zuliani71/LZER0/Hardware/LCC/2021/Project.LCC/SCHEMA ELETTRICO PDF/2721022100A1.4_[No Variations]( LZER0 Core Card ).PDF

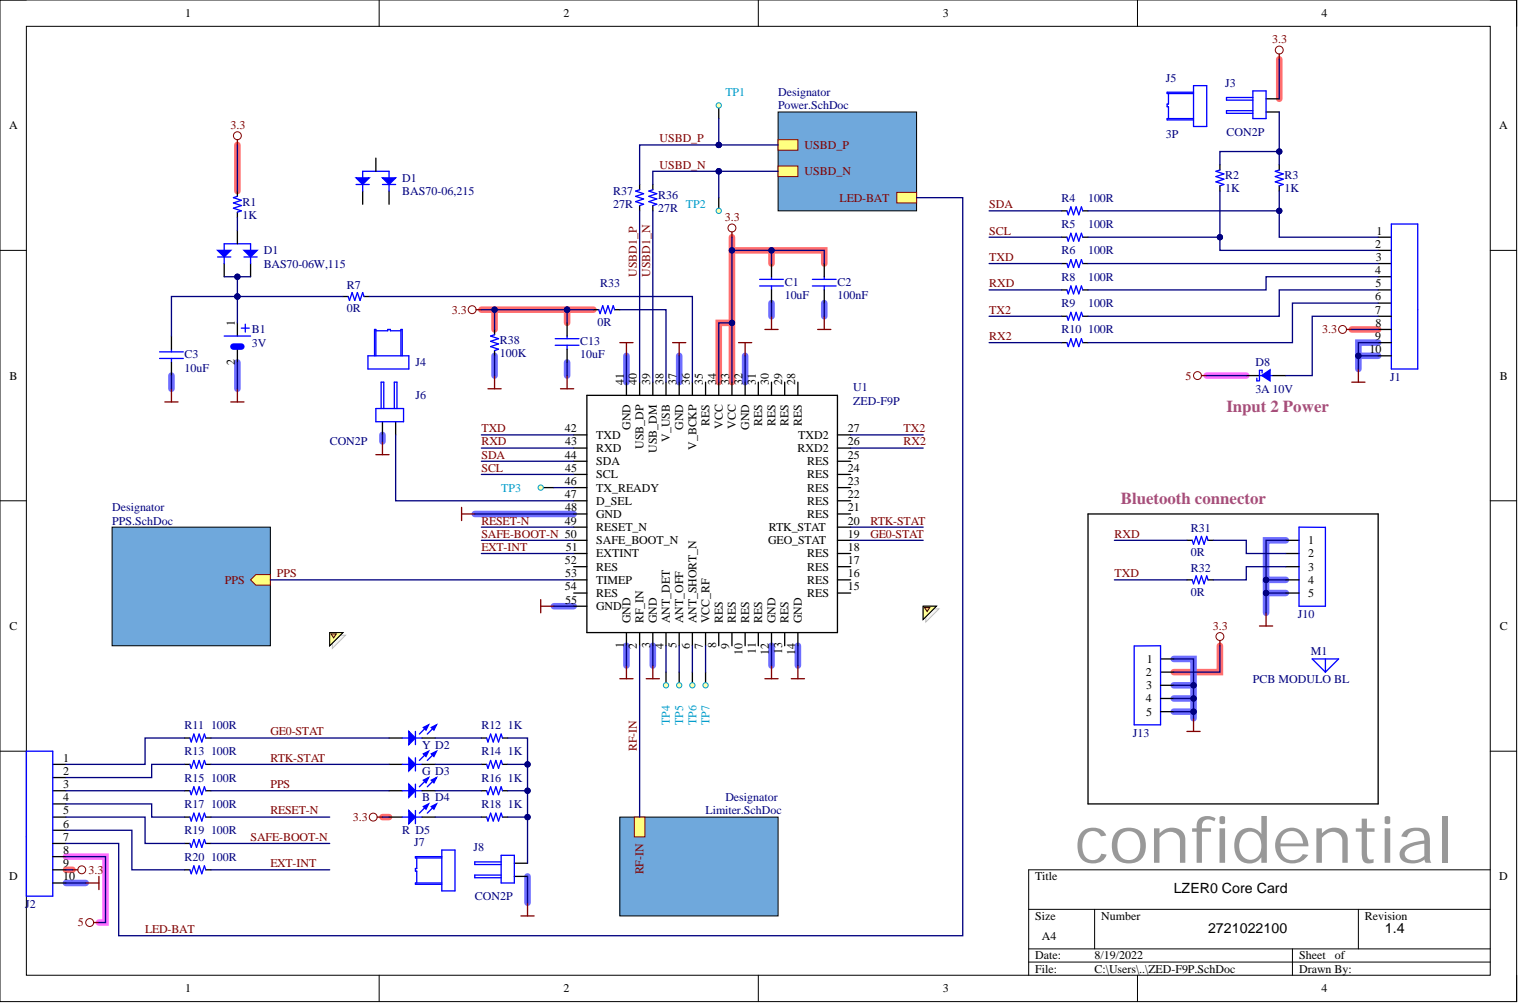
[picture p7: page 1]

GND 14 RES 15 RES 16 RES 17 RES 18

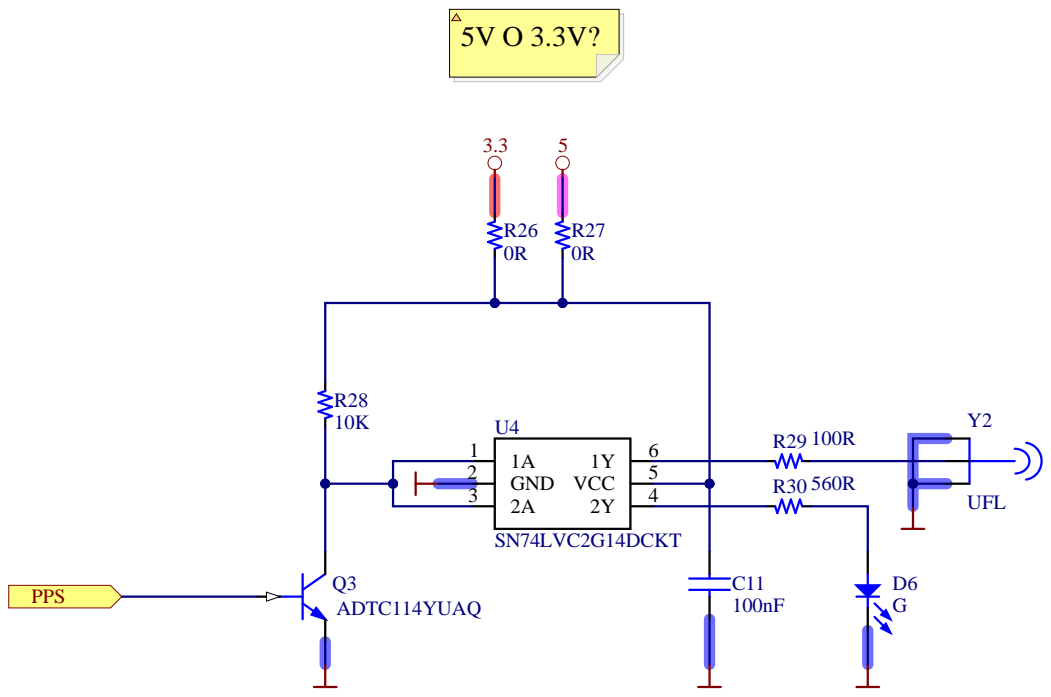
[picture p8: page 2]

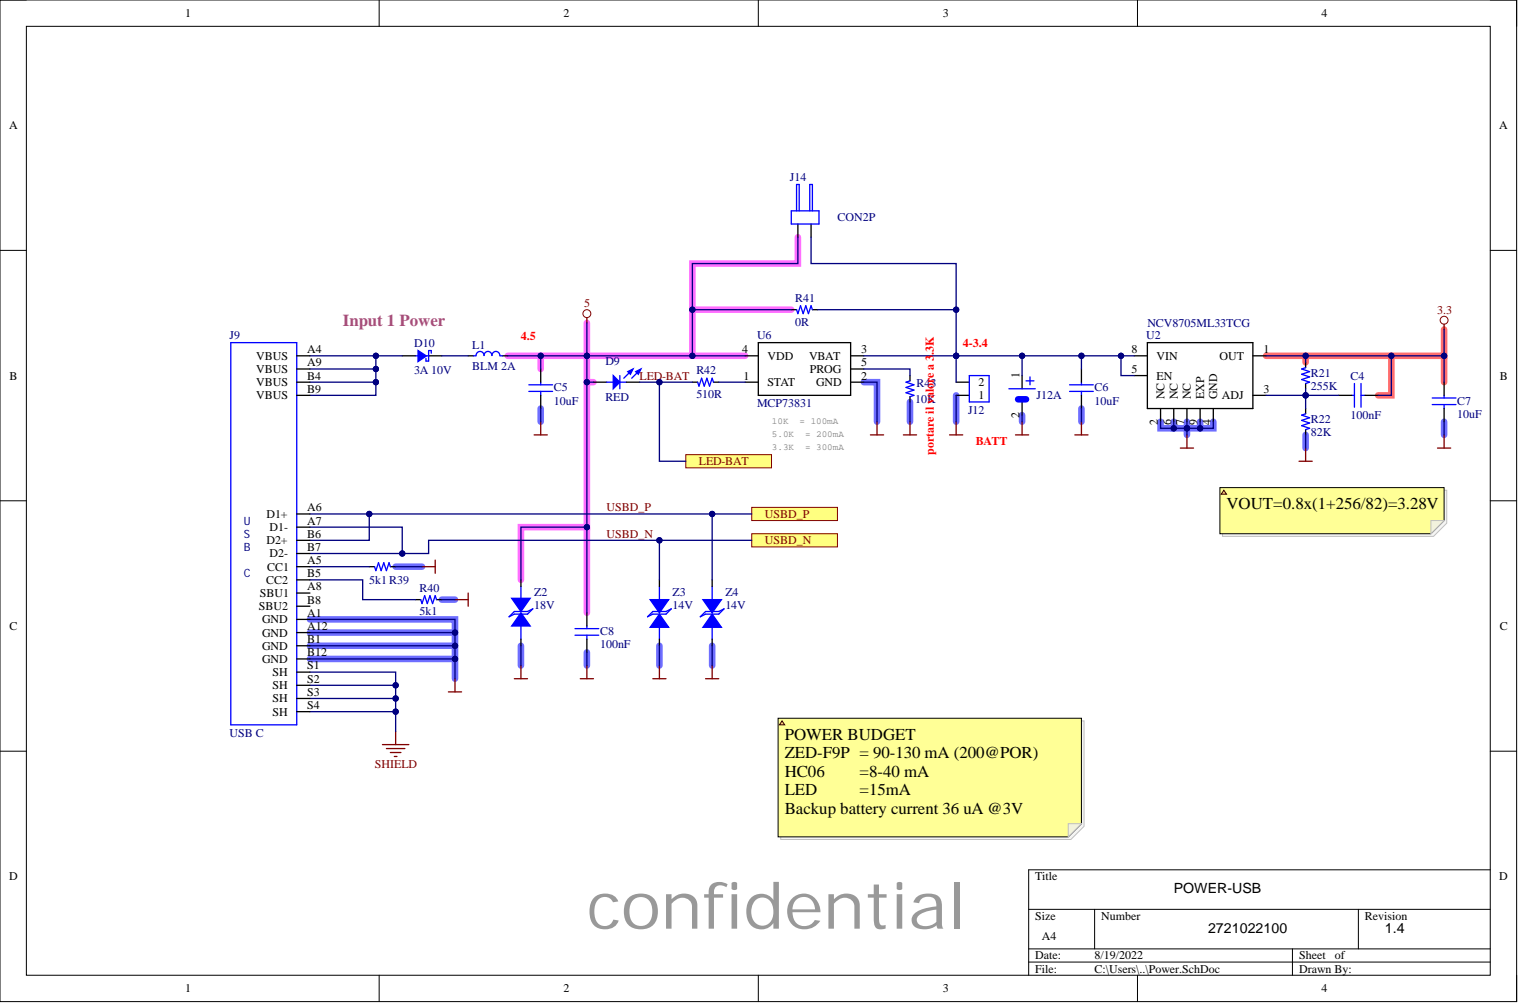
[picture p9: page 3]

POWER BUDGET
ZED-F9P = 90-130 mA (200@POR)
Backup battery current 36 uA @3V

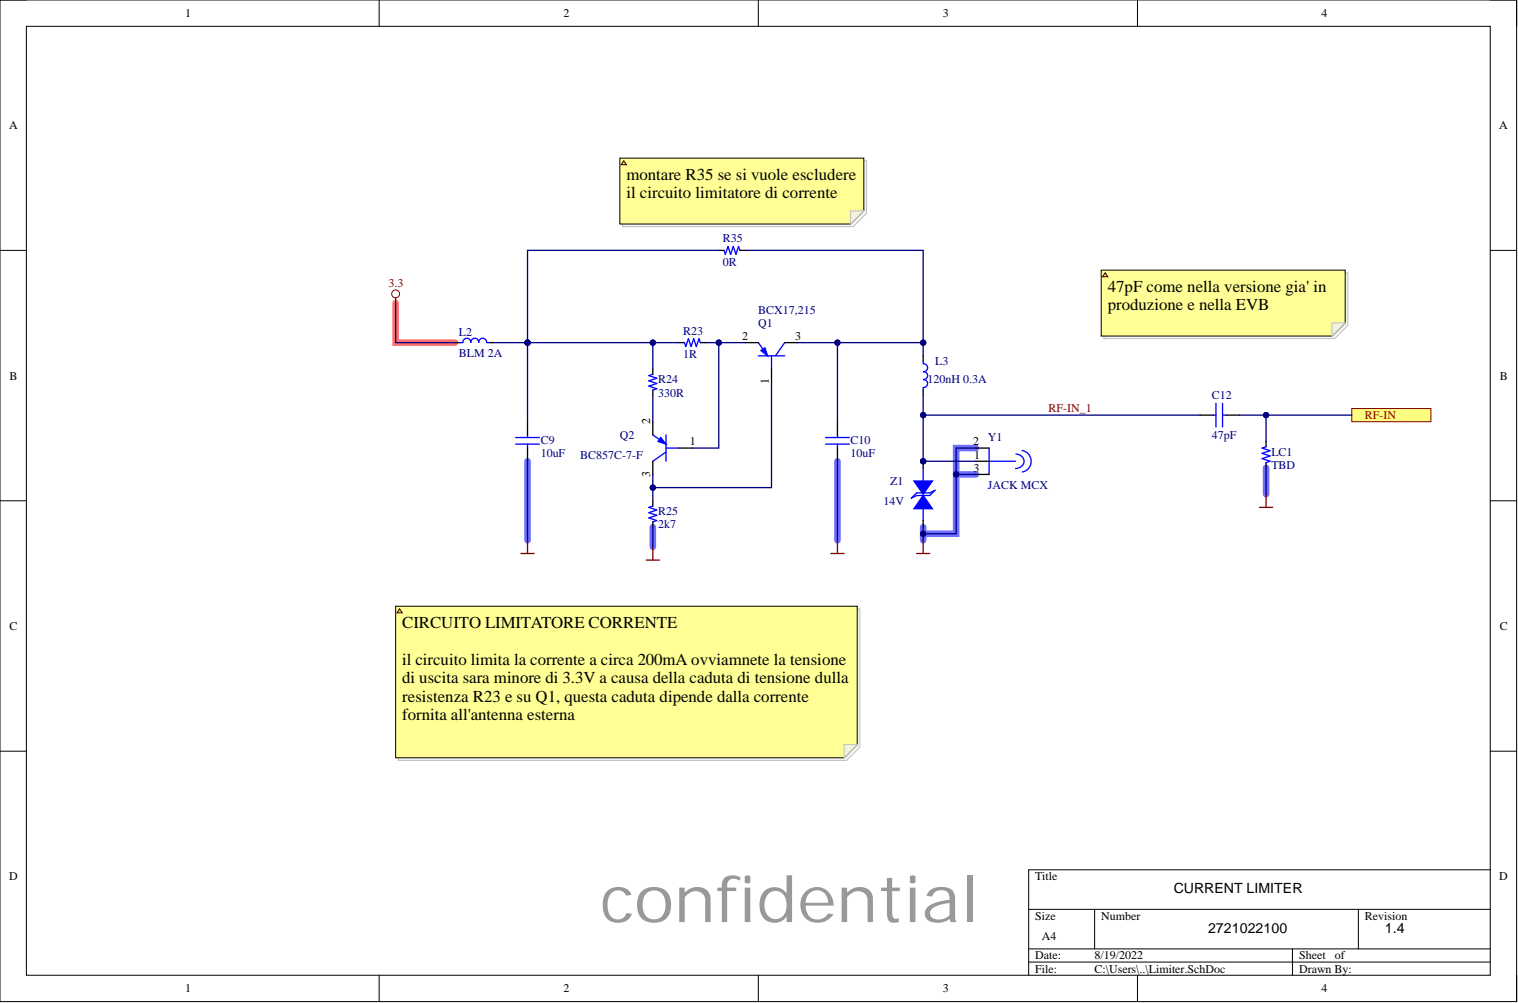
[picture p10: page 4]

montare R35 se si vuole escludere
il circuito limitatore di corrente

47pF come nella versione gia' in
produzione e nella EVB

il circuito limita la corrente a circa 200mA ovviamnete la tensione
di uscita sara minore di 3.3V a causa della caduta di tensione dulla
resistenza R23 e su Q1, questa caduta dipende dalla corrente
fornita all'antenna esterna
