zuliani71/LZER0/Hardware/LCC/2021/Project.BT.module/VARI LATI IN PDF/PCB IN PDF.PDF

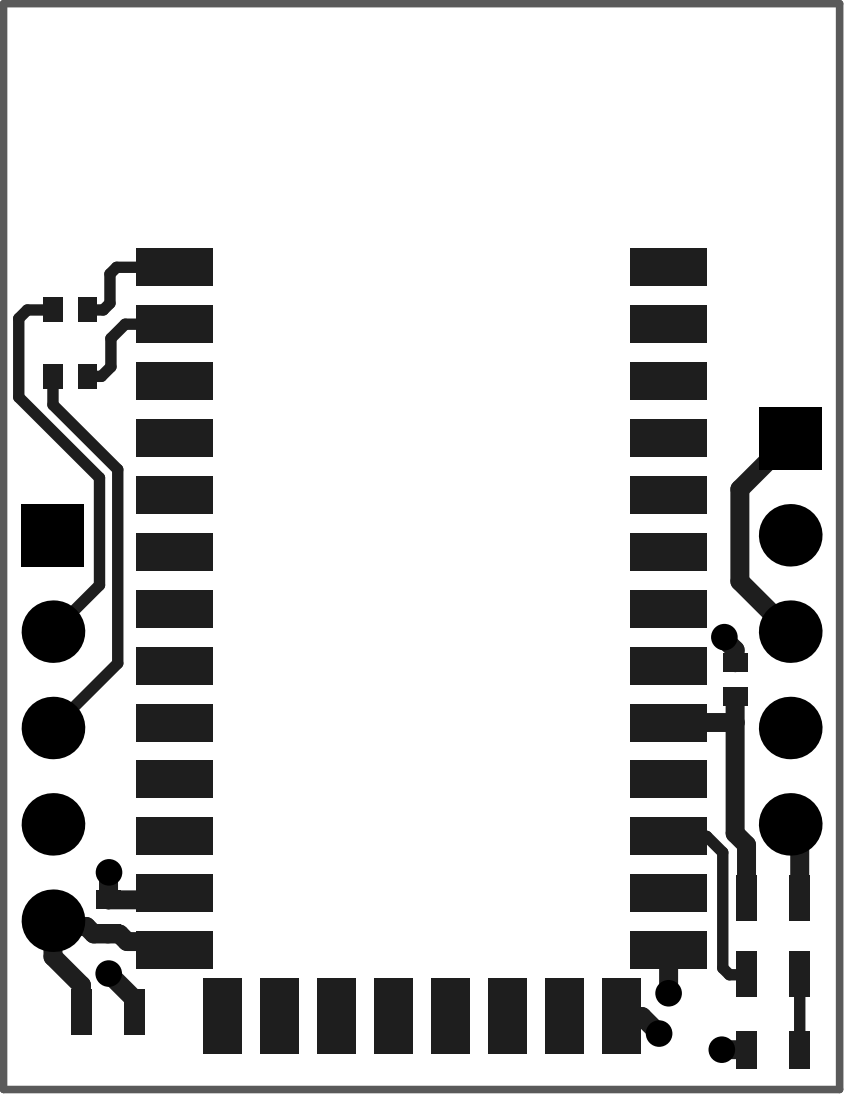
[picture p27: page 1]

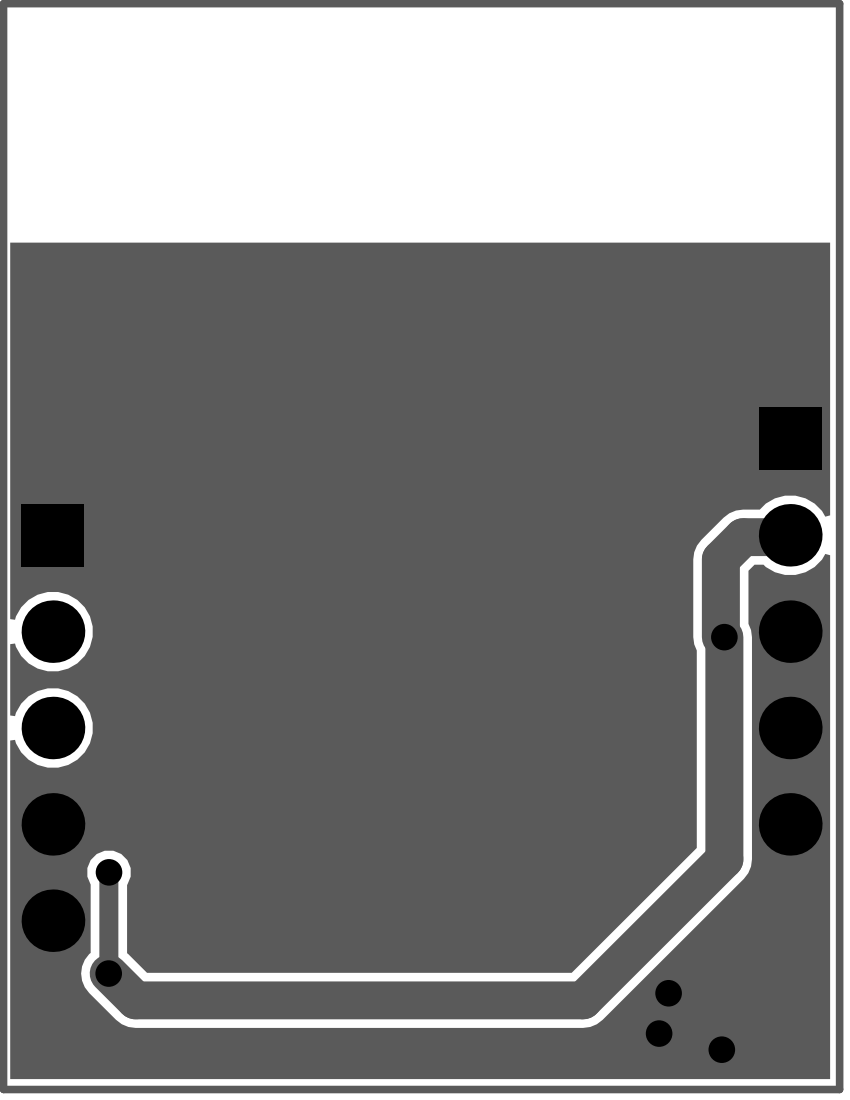
[picture p28: page 2]

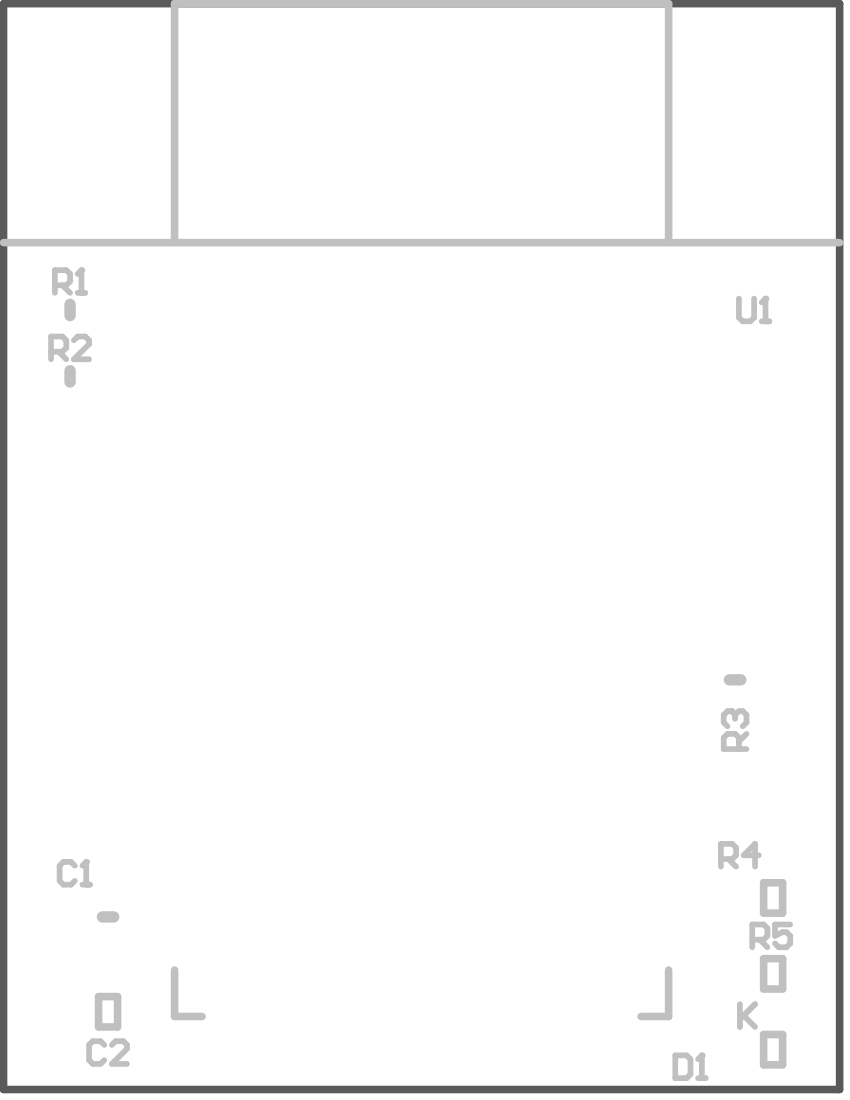
[picture p29: page 3]

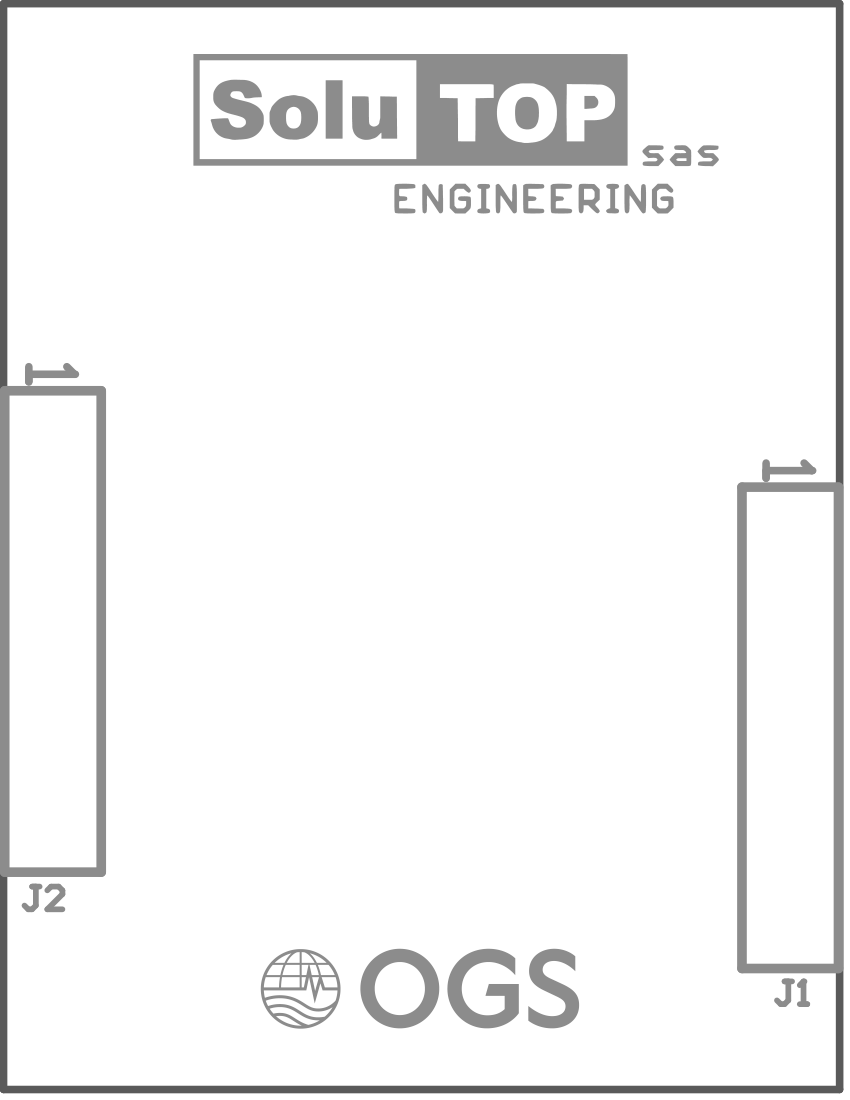
[picture p30: page 4]
