zuliani71/LZER0/Hardware/LCC/2021/Project.LCC/PIANO DI FORATURA PDF/Piano di foratura.PDF

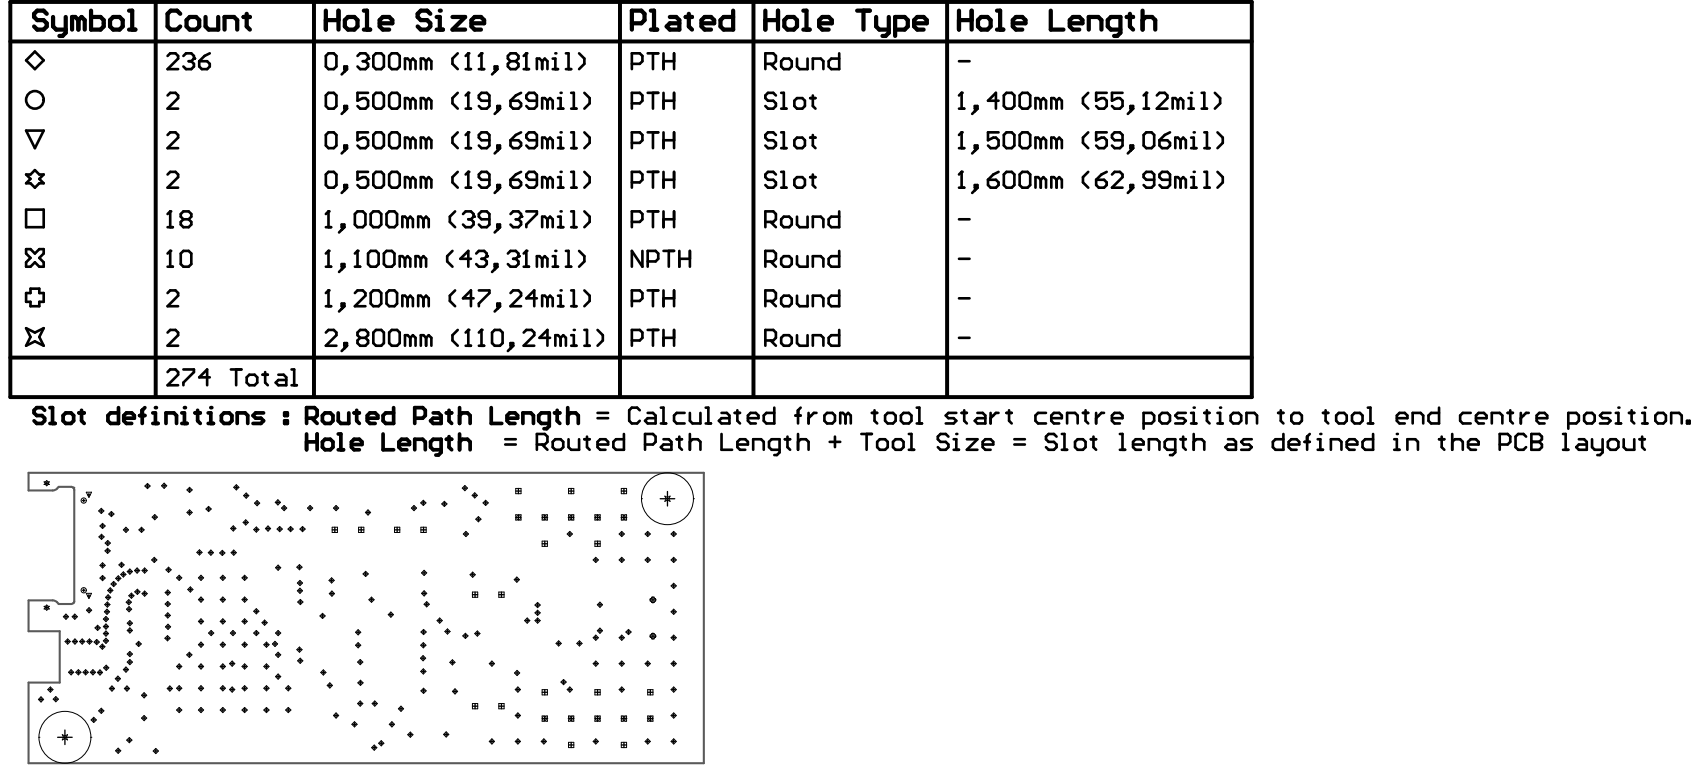
[picture p31: page 1]
