zuliani71/LZER0/Hardware/LCC/2021/Project.LCC/VARI LATI IN PDF/PCB IN PDF.PDF

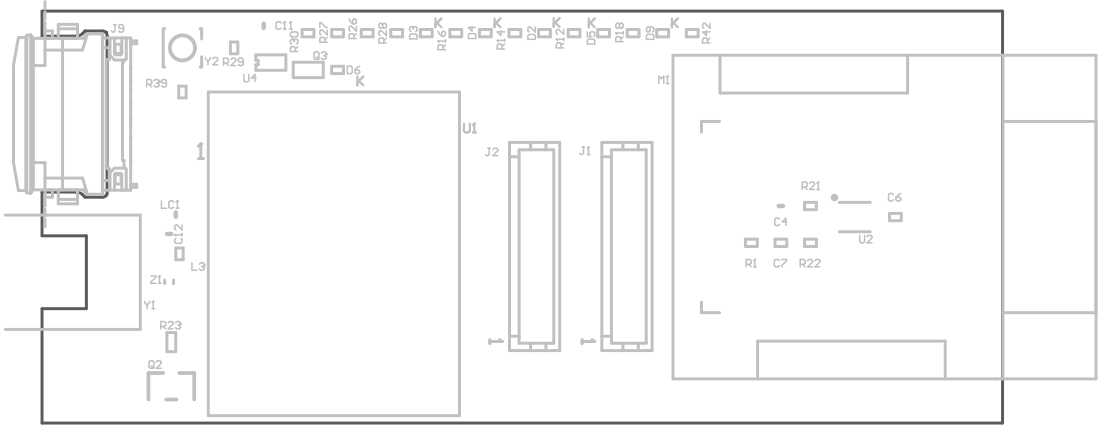
[picture p32: page 1]

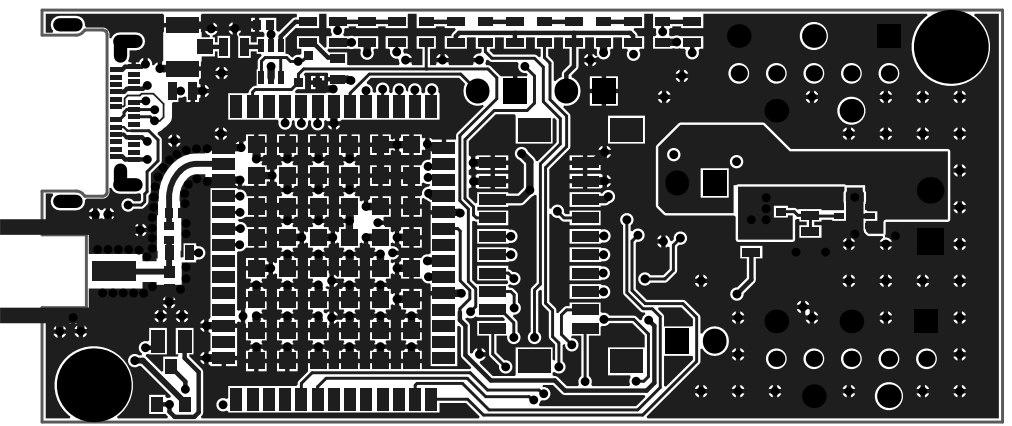
[picture p33: page 2]

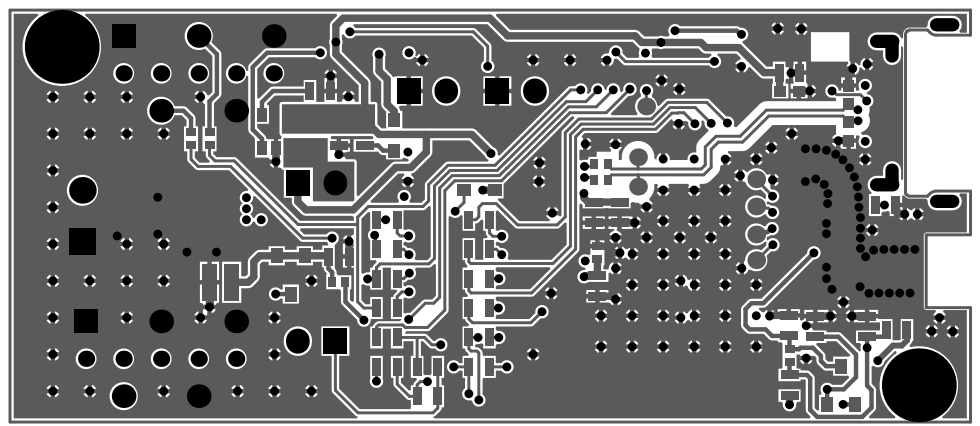
[picture p34: page 3]

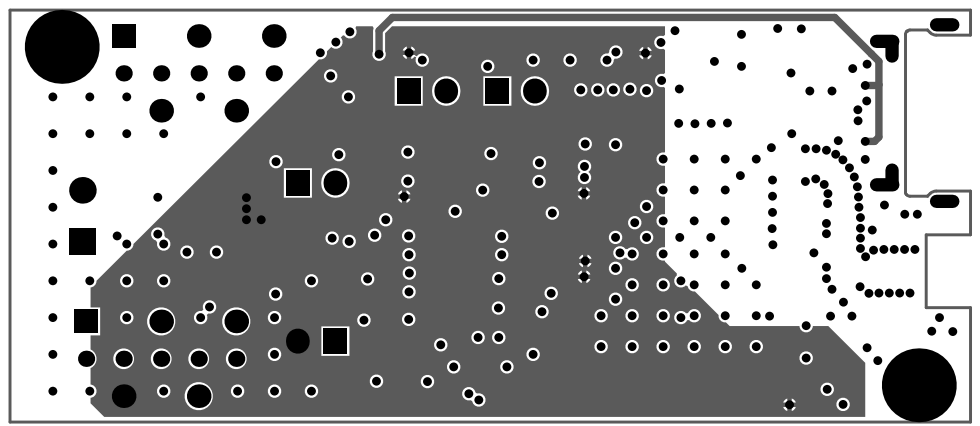
[picture p35: page 4]

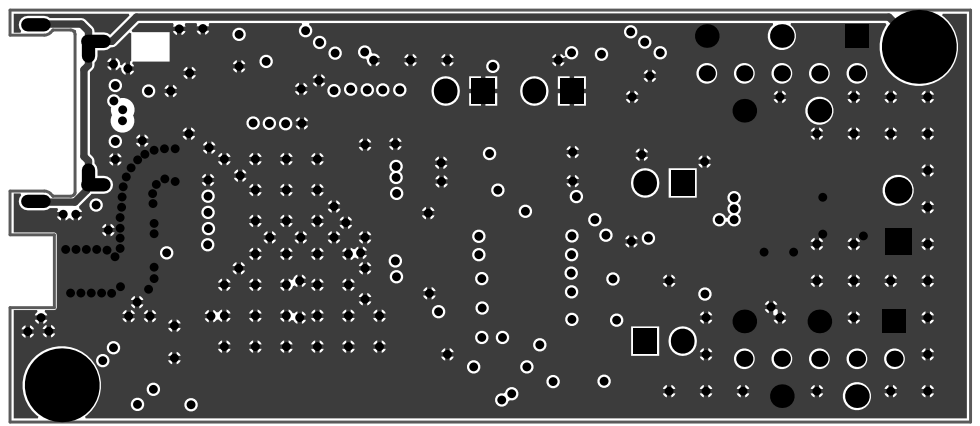
[picture p36: page 5]

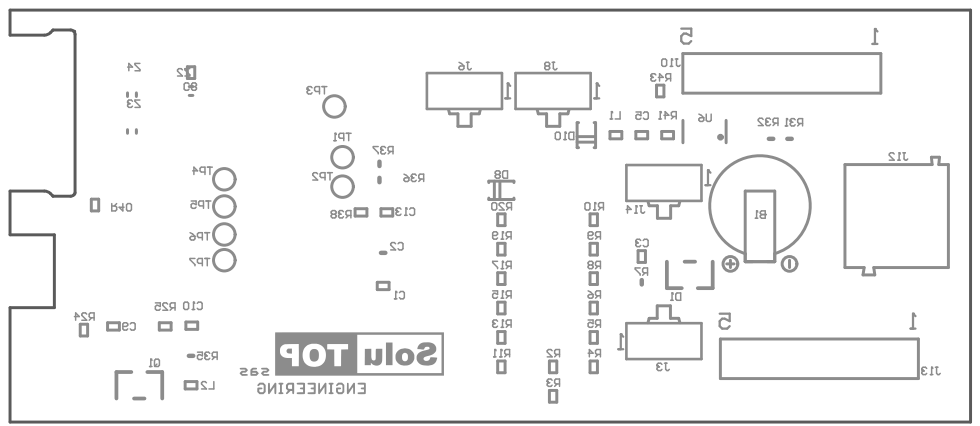
[picture p37: page 6]
