zuliani71/LZER0/Hardware/LCC/2021/Project.LCC/VARI LATI IN PDF/PCB Pianta componenti LC e LS.PDF

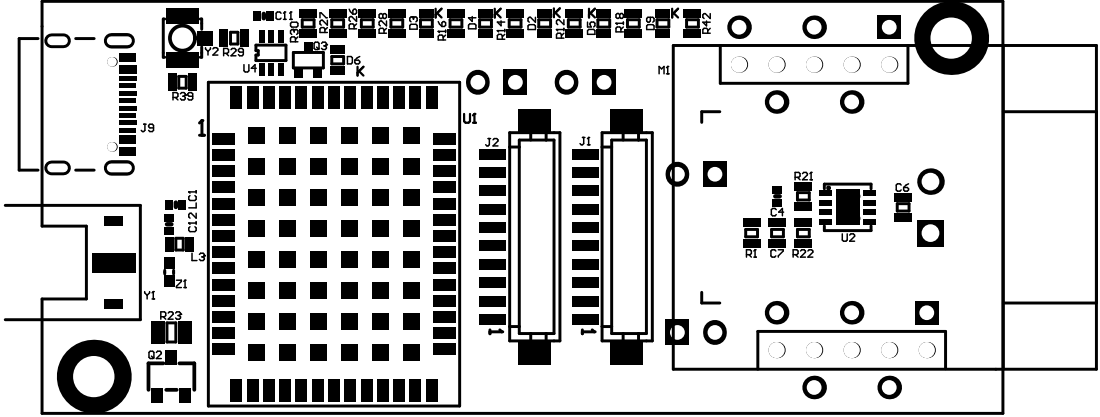
[picture p38: page 1]

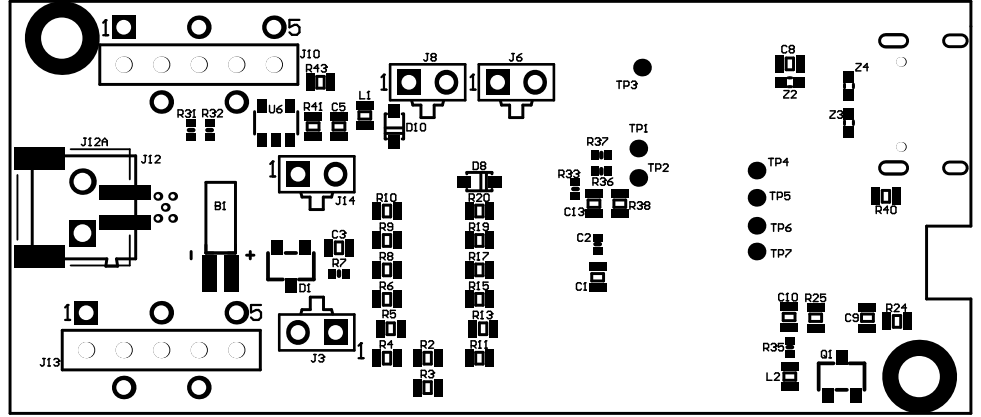
[picture p39: page 2]
